PrasZ24/Project-Microdrone-BSO-ROBOTIKA-2025/arsip/3d and file/Drone_pcb.JPG

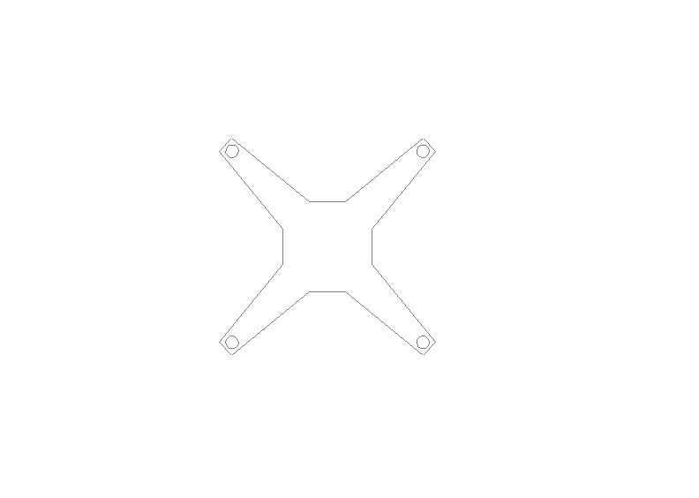
arsip/3d and file/Drone_pcb.JPG
