PrasZ24/Project-Microdrone-BSO-ROBOTIKA-2025/arsip/WhatsApp Image 2025-06-05 at 23.39.49_91929017.jpg

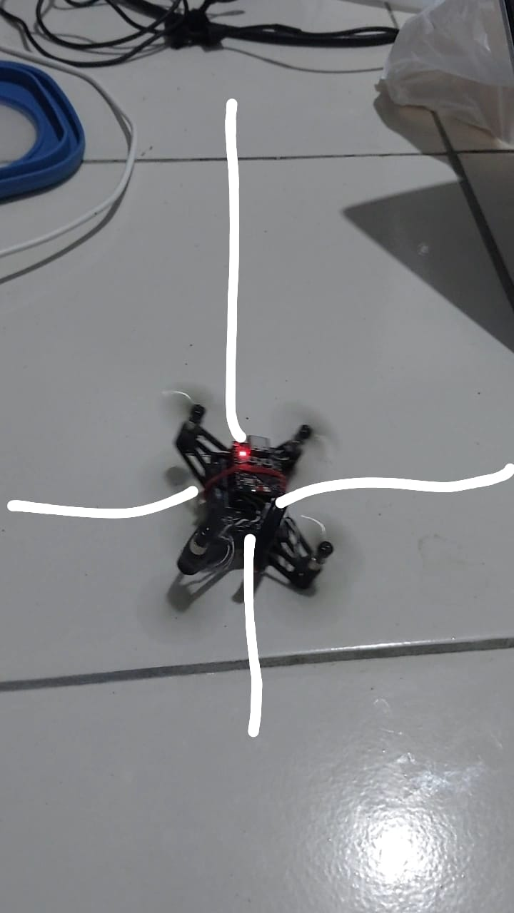
arsip/WhatsApp Image 2025-06-05 at 23.39.49_91929017.jpg
