PrasZ24/Project-Microdrone-BSO-ROBOTIKA-2025/arsip/WhatsApp Image 2025-06-07 at 19.15.57_92371332.jpg

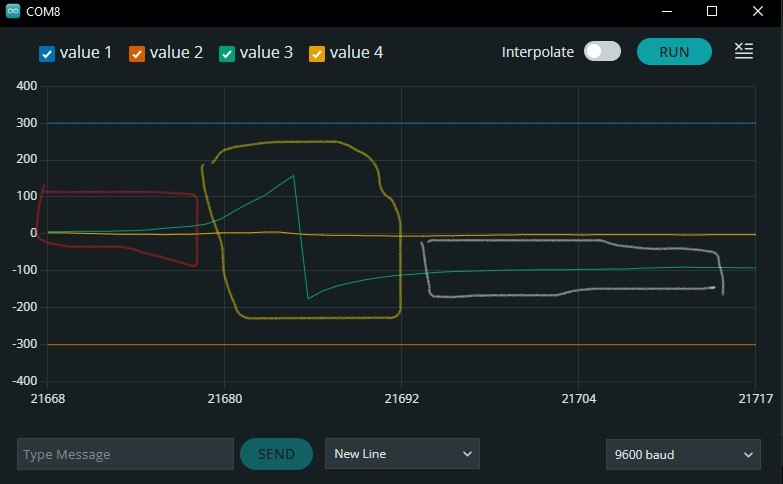
arsip/WhatsApp Image 2025-06-07 at 19.15.57_92371332.jpg
