PrasZ24/Project-Microdrone-BSO-ROBOTIKA-2025/arsip/3d and file/Drone holder.SLDPRT

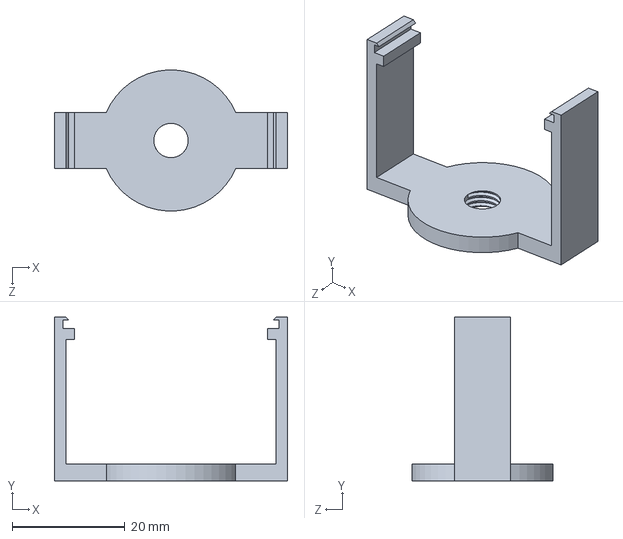
[picture p25: CAD file, 2025-12-12]
arsip/3d and file/Drone holder.SLDPRT
41.3 x 29.0 x 24.9 mm
