PrasZ24/Project-Microdrone-BSO-ROBOTIKA-2025/arsip/3d and file/ESP32-C3 supermini v5.step

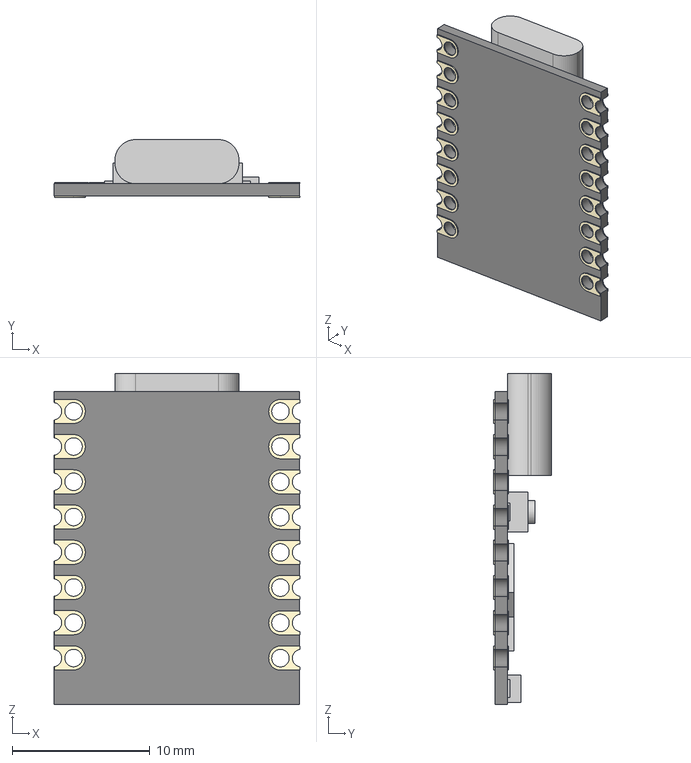
[picture p26: CAD file, 2025-12-12]
arsip/3d and file/ESP32-C3 supermini v5.step
17.8 x 4.20 x 24.0 mm
